aliceDuhem/LaserClosedLoop/LaserControl/general_characteristics.py

#Instead of writing the characteristcis in every function, we take them from this file

class characteristics:
    stepperIncrement=0.45;
    wantedIntensity=0; #get from GUI
    current_motor_angle=0;
    halfWave_transmittance=1;
    cube_ref_trans=1;
    cube_transmittance=1;
    Pd=2;
    
