aliceDuhem/LaserClosedLoop/LaserControl/requiredPowerLaser.py

#This program calculates the power range at which the laser should be
#The ratio takes an infinite value
#Need to take into account the percentage by which the power might drop (can be 25% for NP:YAP) --> need to increase it and start by a lower opened

class requiredPowerLaser:
    wantedPower = power._Characteristics__wantedIntensity;
    
